verynotbad/VNB-Servo-Tester/Docs/Servo Tester - Components.png

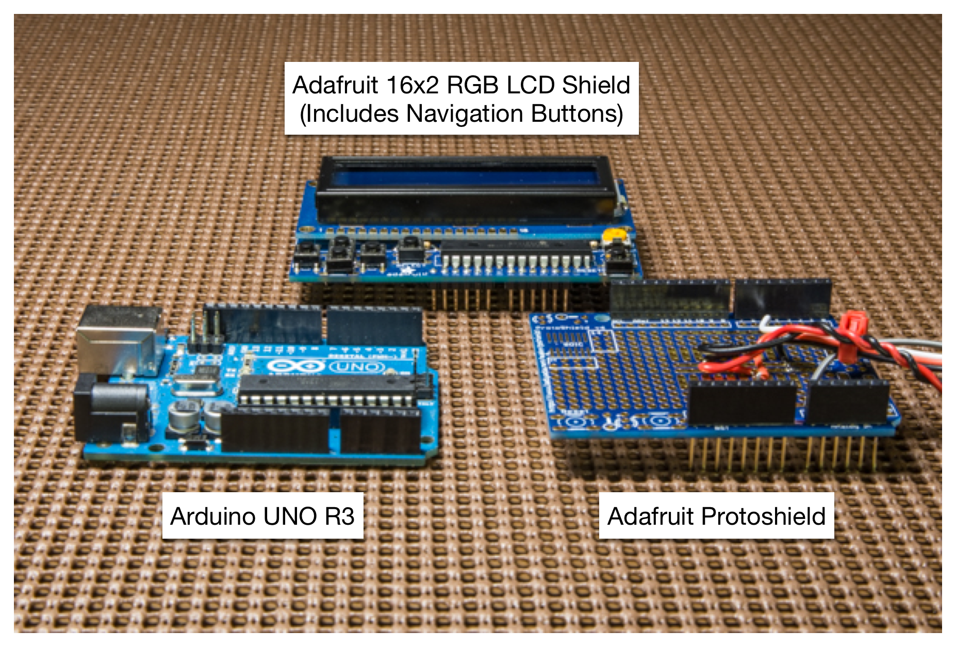
Docs/Servo Tester - Components.png
