verynotbad/VNB-Servo-Tester/Circuit/VNB - Servo Tester - Circuit_bb.png

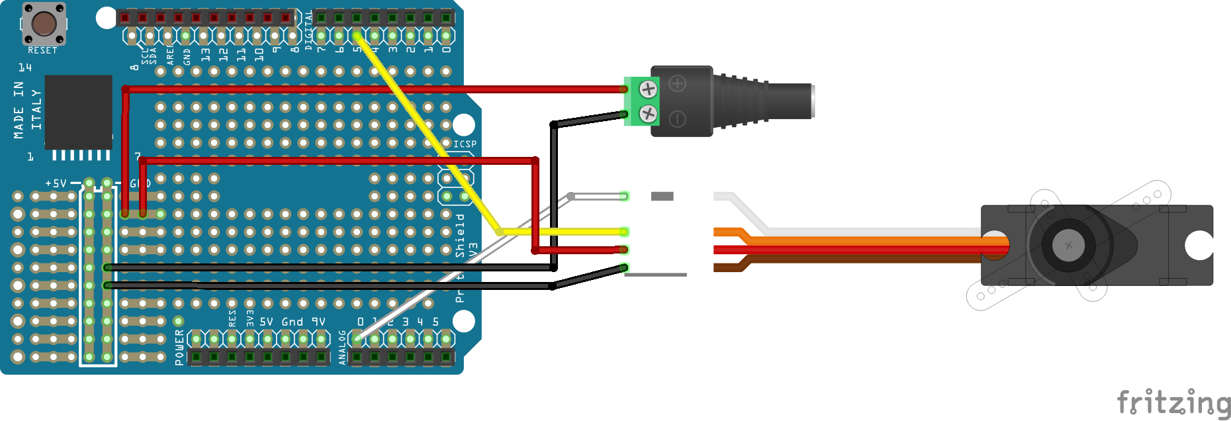
Circuit/VNB - Servo Tester - Circuit_bb.png
