verynotbad/VNB-Servo-Tester/Docs/Servo Tester - 3D Buttons.png

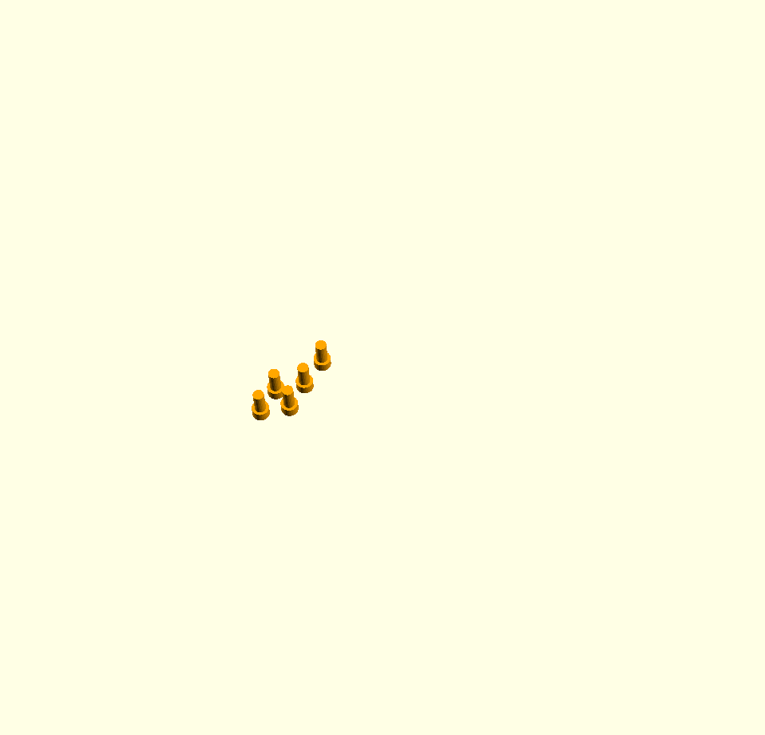
Docs/Servo Tester - 3D Buttons.png
