verynotbad/VNB-Servo-Tester/Docs/Servo Tester - 3D Cradle.png

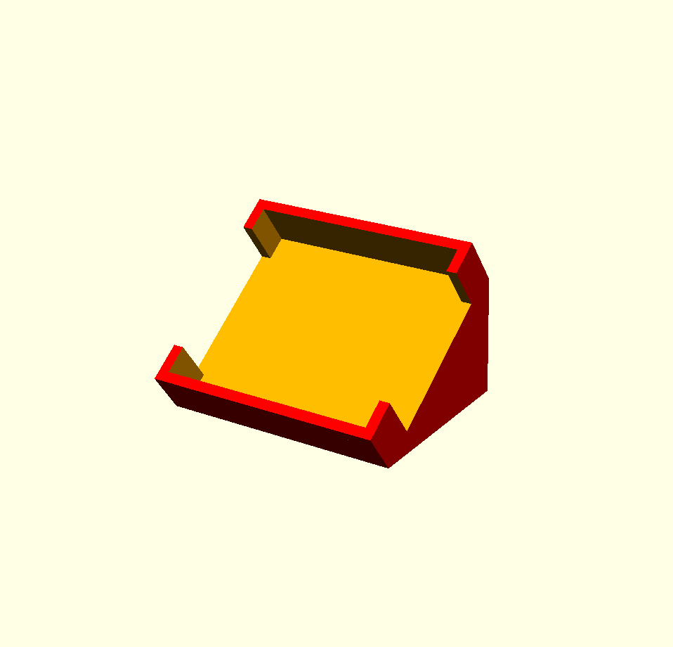
Docs/Servo Tester - 3D Cradle.png
