verynotbad/VNB-Servo-Tester/Docs/Servo Tester - 3D Top.png

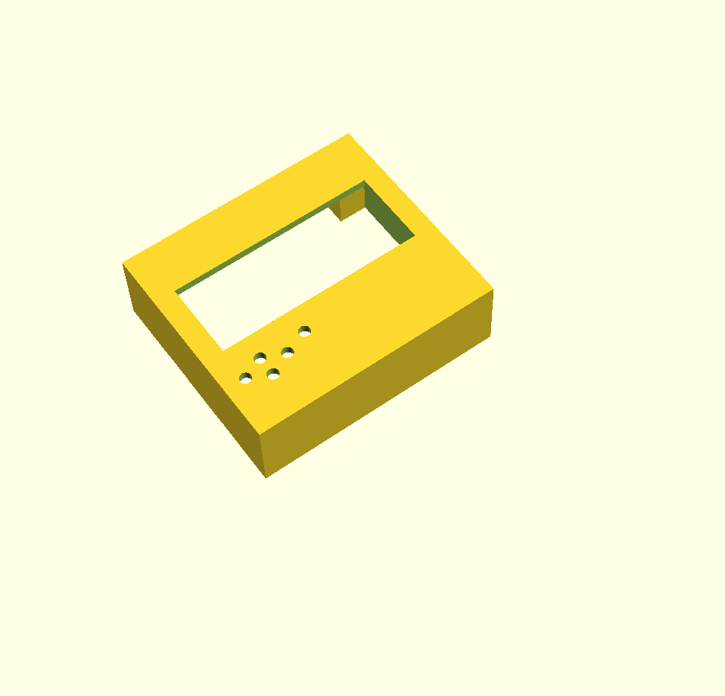
Docs/Servo Tester - 3D Top.png
