verynotbad/VNB-Servo-Tester/Docs/Servo Tester - Breadboard.png

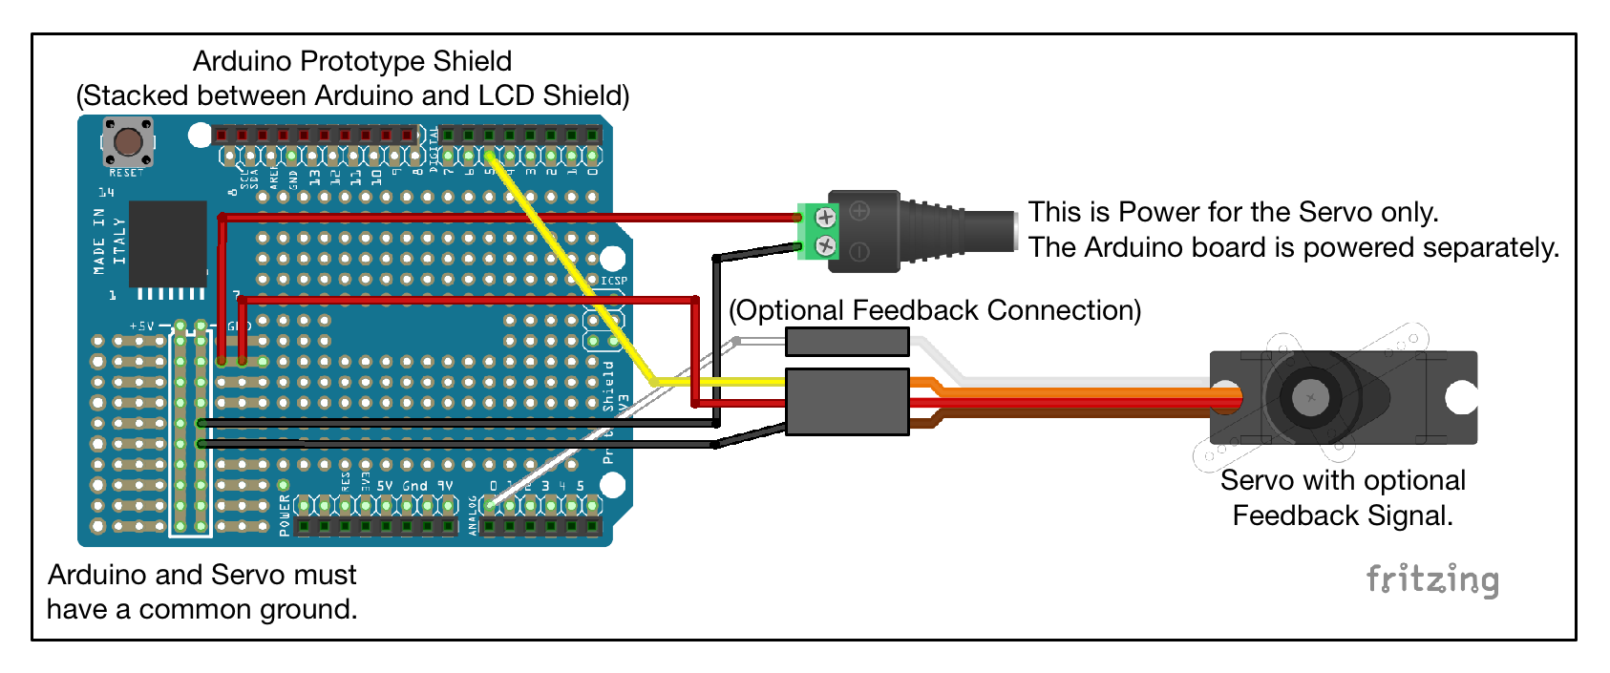
Docs/Servo Tester - Breadboard.png
