verynotbad/VNB-Servo-Tester/Docs/Servo Tester - buttons.png

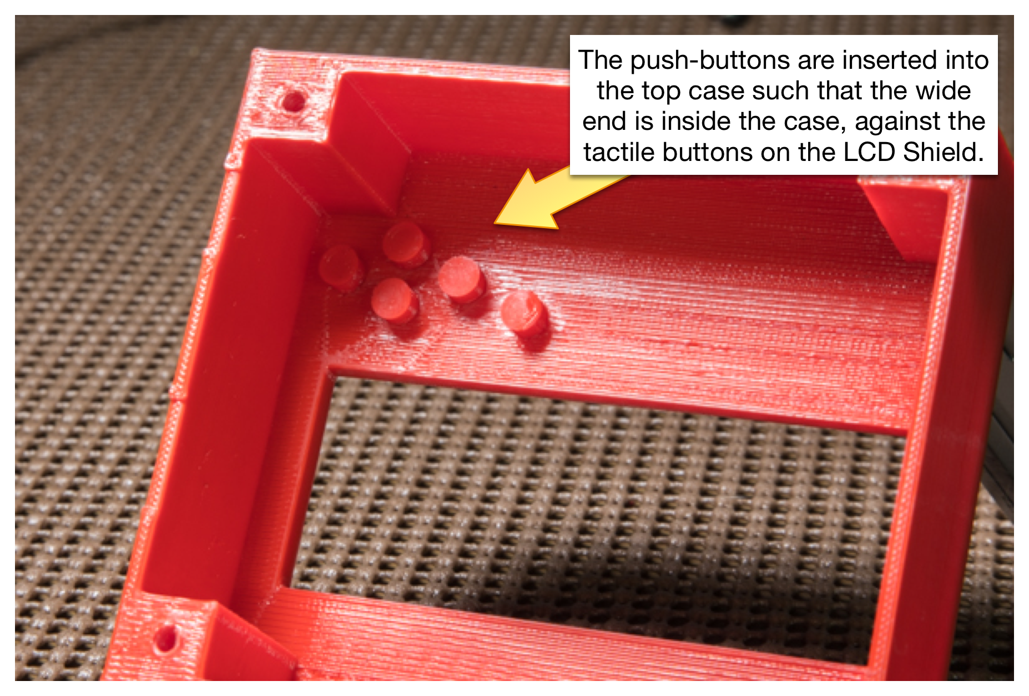
Docs/Servo Tester - buttons.png
