verynotbad/VNB-Servo-Tester/Docs/Servo Tester - Cables.png

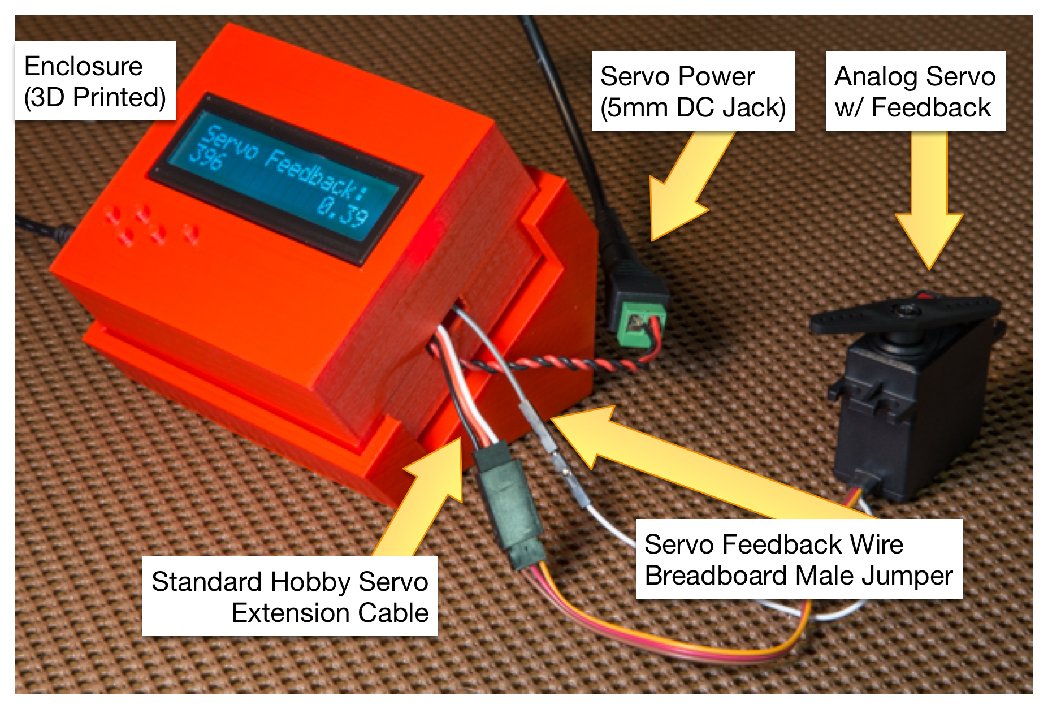
Docs/Servo Tester - Cables.png
