verynotbad/VNB-Servo-Tester/Docs/Servo Tester - Stack.png

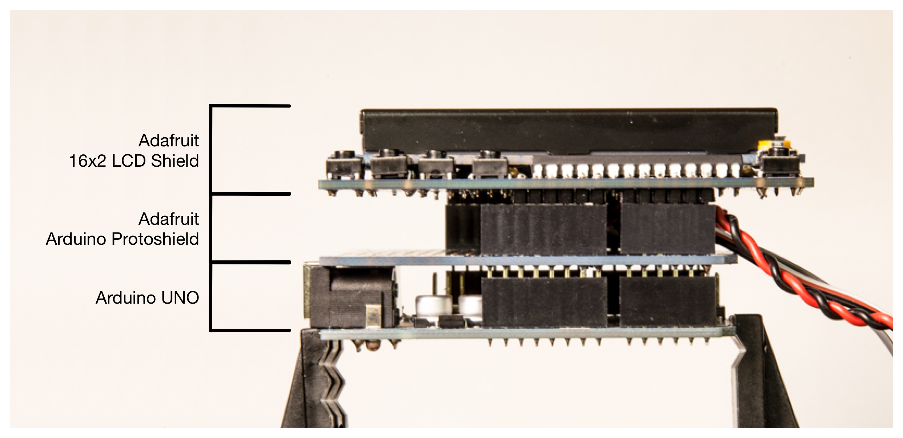
Docs/Servo Tester - Stack.png
