verynotbad/VNB-Servo-Tester/Docs/Servo Tester - Top View.png

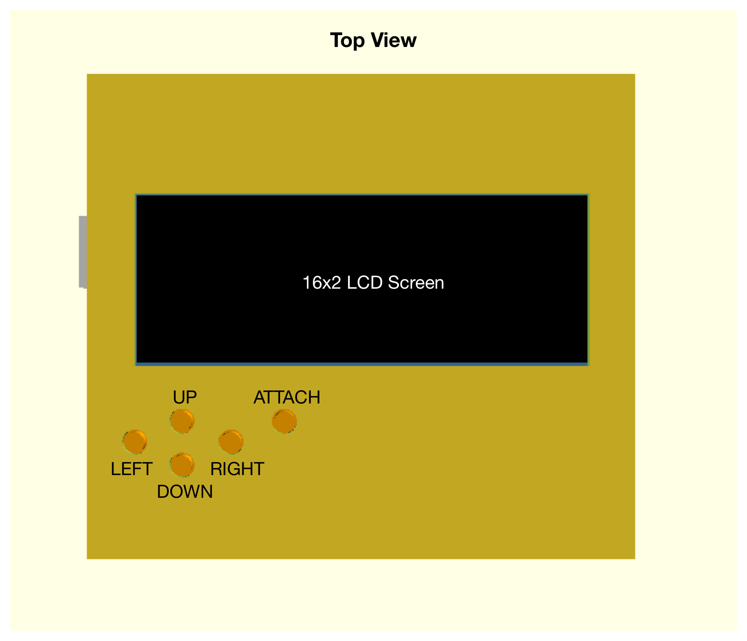
Docs/Servo Tester - Top View.png
