verynotbad/VNB-Servo-Tester/Photos/VNB-Servo-Tester-1.jpg

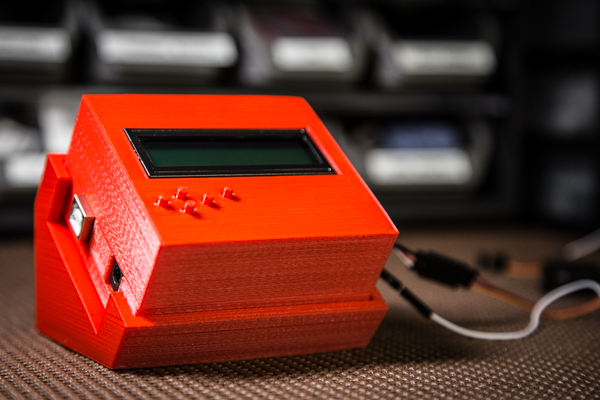
Photos/VNB-Servo-Tester-1.jpg
