verynotbad/VNB-Servo-Tester/Photos/VNB-Servo-Tester-2.jpg

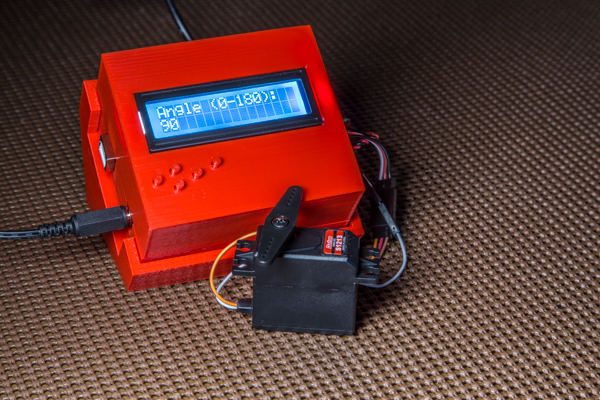
Photos/VNB-Servo-Tester-2.jpg
