verynotbad/VNB-Servo-Tester/Photos/VNB-Servo-Tester-3.jpg

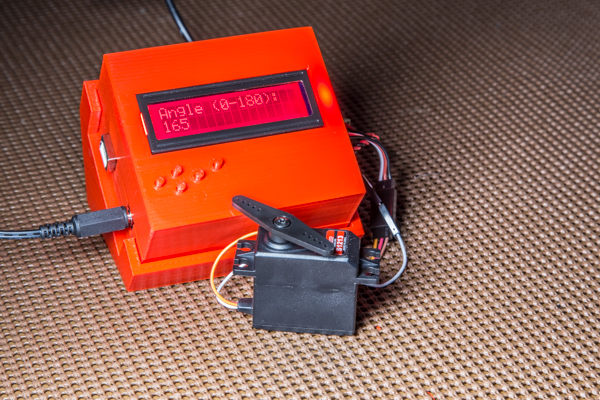
Photos/VNB-Servo-Tester-3.jpg
