verynotbad/VNB-Servo-Tester/Photos/VNB-Servo-Tester-9.jpg

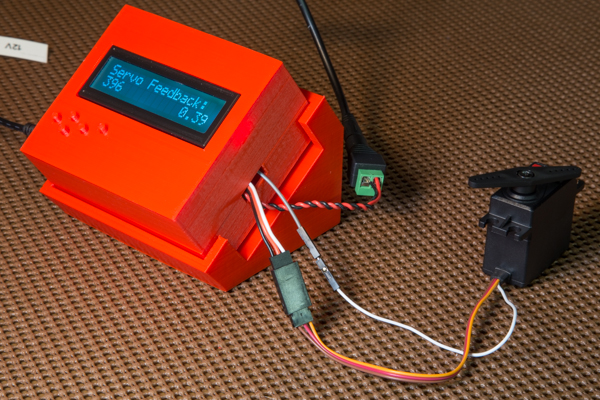
Photos/VNB-Servo-Tester-9.jpg
