verynotbad/VNB-Servo-Tester/Photos/VNB-Servo-Tester-11.jpg

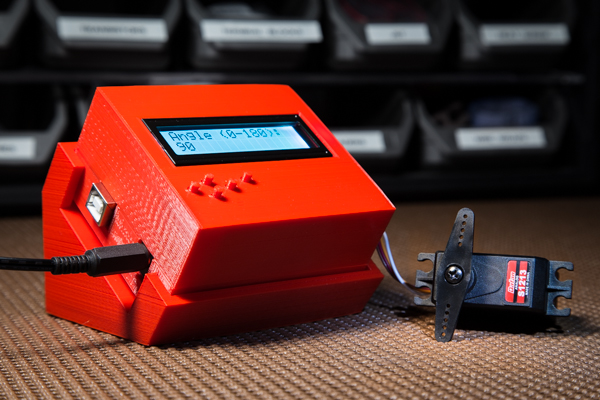
Photos/VNB-Servo-Tester-11.jpg
