verynotbad/VNB-Servo-Tester/Photos/VNB-Servo-Tester-12.jpg

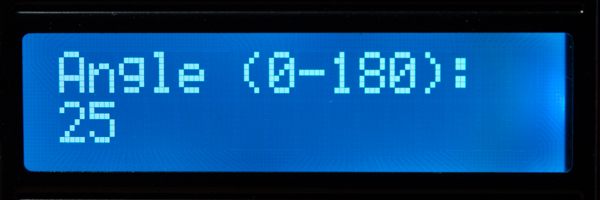
Photos/VNB-Servo-Tester-12.jpg
