verynotbad/VNB-Servo-Tester/Photos/VNB-Servo-Tester-13.jpg

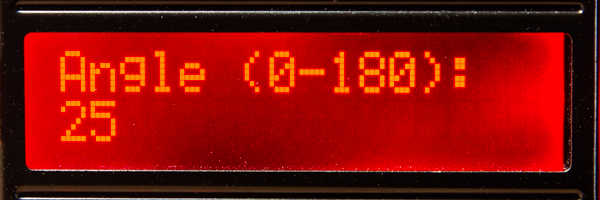
Photos/VNB-Servo-Tester-13.jpg
