verynotbad/VNB-Servo-Tester/Photos/VNB-Servo-Tester-14.jpg

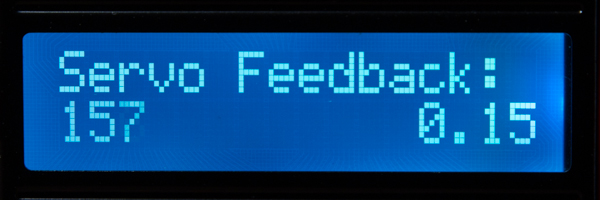
Photos/VNB-Servo-Tester-14.jpg
