verynotbad/VNB-Servo-Tester/Photos/VNB-Servo-Tester-15.jpg

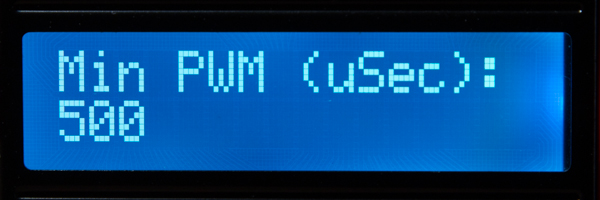
Photos/VNB-Servo-Tester-15.jpg
