verynotbad/VNB-Servo-Tester/Photos/VNB-Servo-Tester-17.jpg

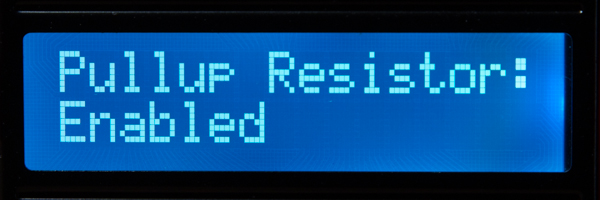
Photos/VNB-Servo-Tester-17.jpg
