verynotbad/VNB-Servo-Tester/Photos/VNB-Servo-Tester-18.jpg

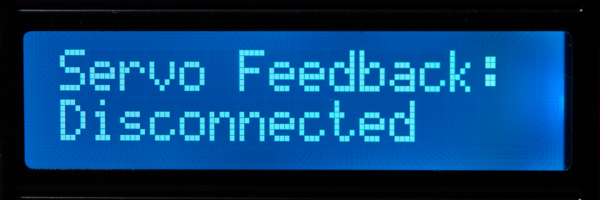
Photos/VNB-Servo-Tester-18.jpg
