verynotbad/VNB-Servo-Tester/Photos/VNB-Servo-Tester-19.jpg

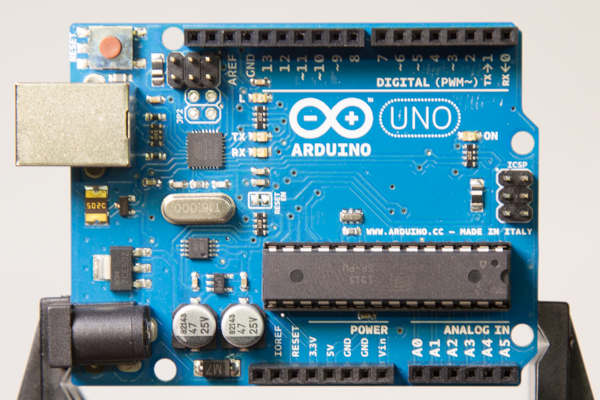
Photos/VNB-Servo-Tester-19.jpg
