verynotbad/VNB-Servo-Tester/Photos/VNB-Servo-Tester-20.jpg

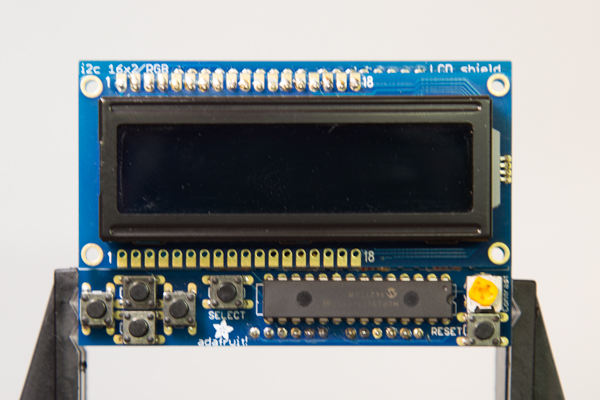
Photos/VNB-Servo-Tester-20.jpg
