verynotbad/VNB-Servo-Tester/Photos/VNB-Servo-Tester-31.jpg

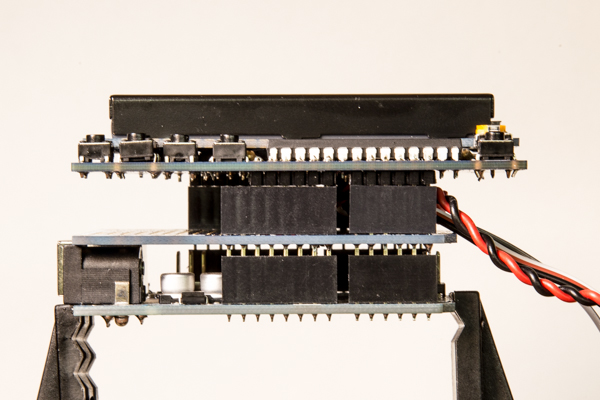
Photos/VNB-Servo-Tester-31.jpg
