verynotbad/VNB-Servo-Tester/Photos/VNB-Servo-Tester-32.jpg

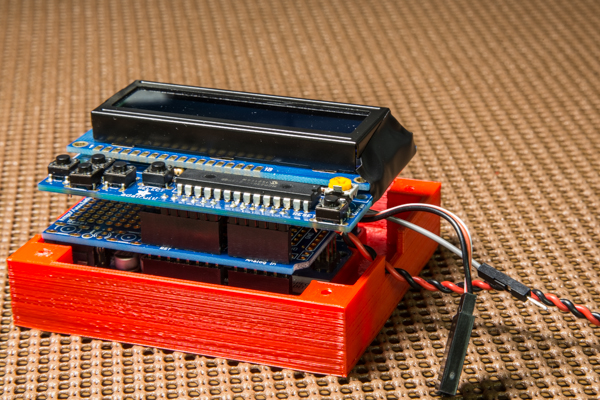
Photos/VNB-Servo-Tester-32.jpg
